Miq1/Dewair/Extras/Enclosure/Dewair_klein_V2-Deckel.stl

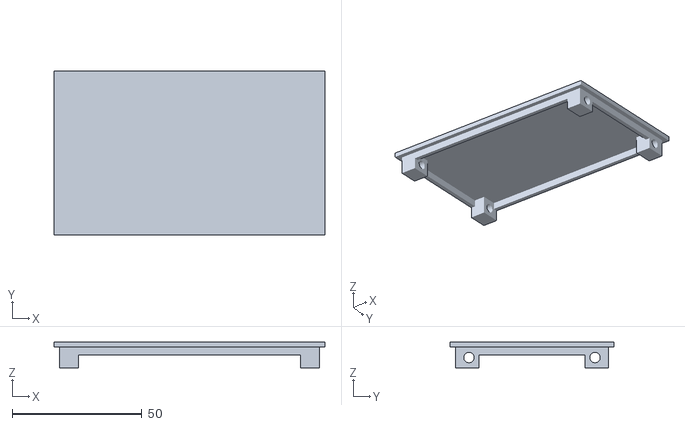
[picture p27: CAD file, 2022-12-30]
Extras/Enclosure/Dewair_klein_V2-Deckel.stl
104.3 x 63.2 x 10.0
