Miq1/Dewair/Extras/Enclosure/Dewair_klein_V2-Unterschale.stl

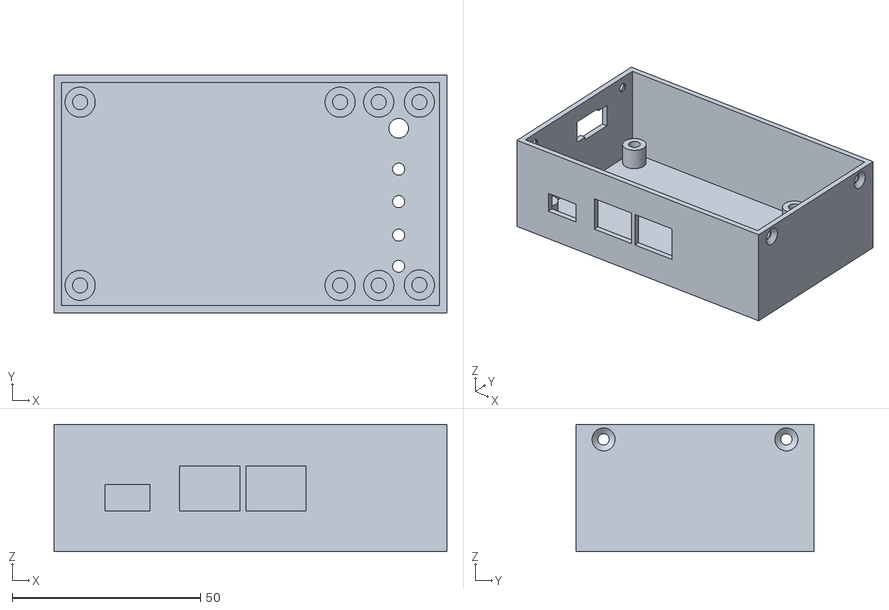
[picture p28: CAD file, 2022-12-30]
Extras/Enclosure/Dewair_klein_V2-Unterschale.stl
104.3 x 63.2 x 33.8
