Miq1/Dewair/Extras/Enclosure/Dewair_klein_V2-LED-Riser.stl

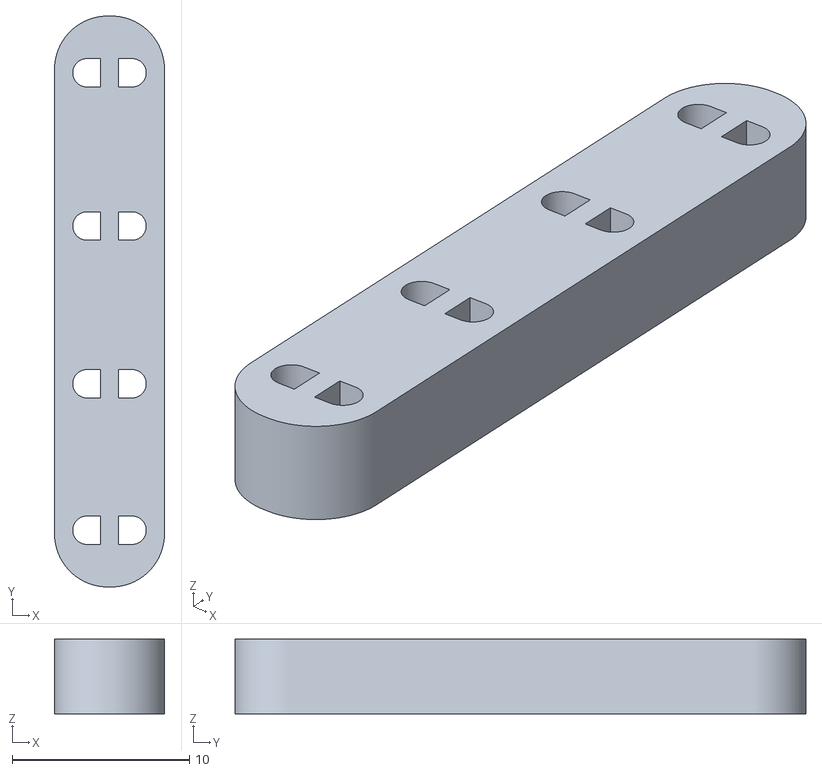
[picture p29: CAD file, 2022-12-30]
Extras/Enclosure/Dewair_klein_V2-LED-Riser.stl
6.20 x 32.2 x 4.20
