Miq1/Dewair/Extras/Enclosure/Dewair_klein_V2-Taste.stl

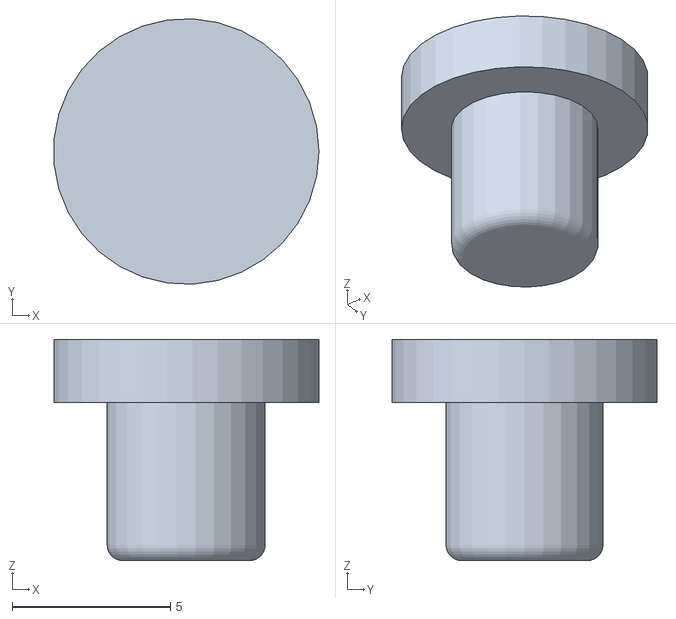
[picture p30: CAD file, 2022-12-30]
Extras/Enclosure/Dewair_klein_V2-Taste.stl
8.38 x 8.39 x 7.00
